p-kowa/SmartErgoMeter/pictures/rotary potentiometer.jpg

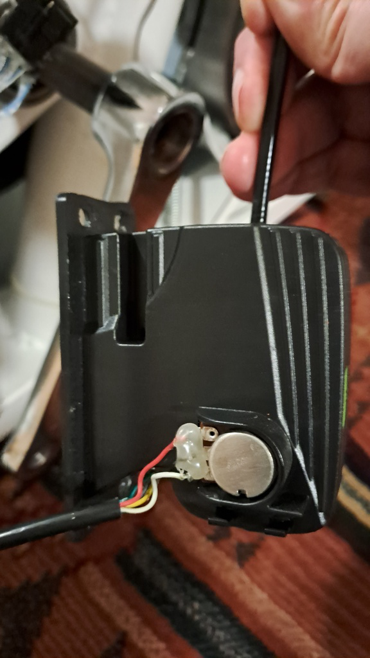
pictures/rotary potentiometer.jpg
